astuder/duckglow/code/lookup.h

uint16_t sine[] = {
	0,0,2,5,9,15,22,30,
	39,49,61,74,88,104,120,138,
	157,178,199,222,246,271,298,325,
	354,384,416,448,482,517,553,591,
	629,669,710,752,796,840,886,933,
	982,1031,1082,1133,1186,1241,1296,1353,
	1410,1469,1530,1591,1653,1717,1782,1848,
	1915,1983,2053,2123,2195,2268,2342,2417,
	2494,2571,2650,2730,2811,2893,2976,3060,
	3146,3232,3320,3408,3498,3589,3681,3774,
	3869,3964,4060,4158,4256,4356,4457,4559,
	4661,4765,4870,4976,5083,5191,5301,5411,
	5522,5634,5747,5862,5977,6093,6210,6329,
	6448,6568,6690,6812,6935,7059,7184,7310,
	7437,7566,7694,7824,7955,8087,8220,8353,
	8488,8623,8760,8897,9035,9174,9314,9455,
	9597,9740,9883,10027,10173,10319,10466,10613,
	10762,10911,11061,11212,11364,11517,11670,11825,
	11980,12136,12292,12449,12608,12766,12926,13086,
	13248,13409,13572,13735,13899,14064,14230,14396,
	14563,14730,14898,15067,15237,15407,15578,15749,
	15921,16094,16268,16442,16616,16791,16967,17144,
	17321,17498,17677,17855,18035,18215,18395,18576,
	18757,18939,19122,19305,19489,19673,19857,20042,
	20228,20414,20600,20787,20974,21162,21351,21539,
	21728,21918,22108,22298,22489,22680,22871,23063,
	23255,23448,23641,23834,24028,24222,24416,24611,
	24806,25001,25196,25392,25588,25784,25981,26178,
	26375,26572,26770,26967,27165,27364,27562,27761,
	27959,28158,28358,28557,28756,28956,29156,29356,
	29556,29756,29956,30156,30357,30557,30758,30959,
	31160,31360,31561,31762,31963,32164,32365,32566,
	32767,32969,33170,33371,33572,33773,33974,34175,
	34375,34576,34777,34978,35178,35379,35579,35779,
	35979,36179,36379,36579,36779,36978,37177,37377,
	37576,37774,37973,38171,38370,38568,38765,38963,
	39160,39357,39554,39751,39947,40143,40339,40534,
	40729,40924,41119,41313,41507,41701,41894,42087,
	42280,42472,42664,42855,43046,43237,43427,43617,
	43807,43996,44184,44373,44561,44748,44935,45121,
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
	};
uint16_t sine_size = 1152;
